Plantenna/Stomata-microscope/IMG_2707.jpg

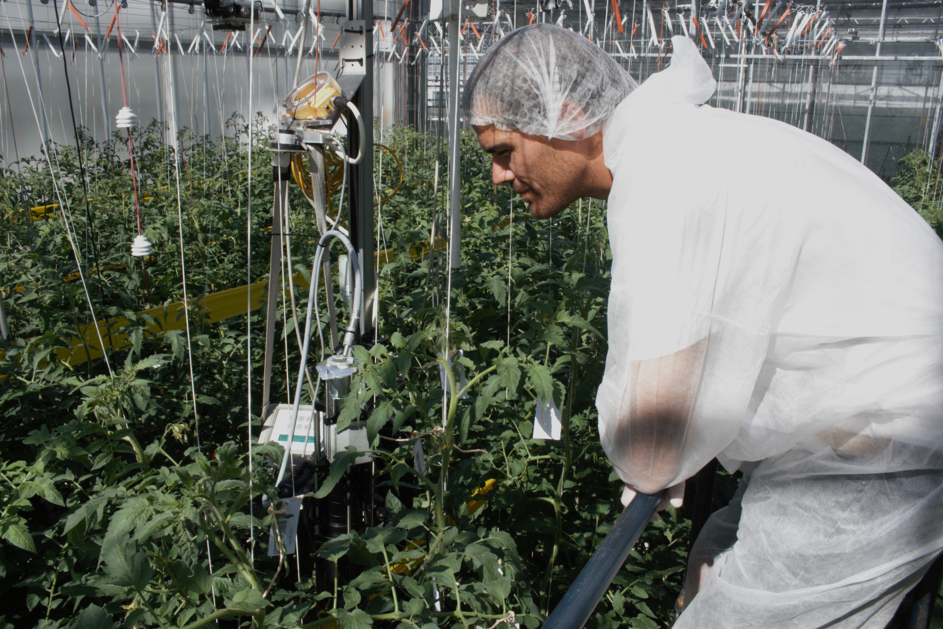
IMG_2707.jpg
