Plantenna/Stomata-microscope/stomata microscope mechanical/3d printed cover.SLDPRT

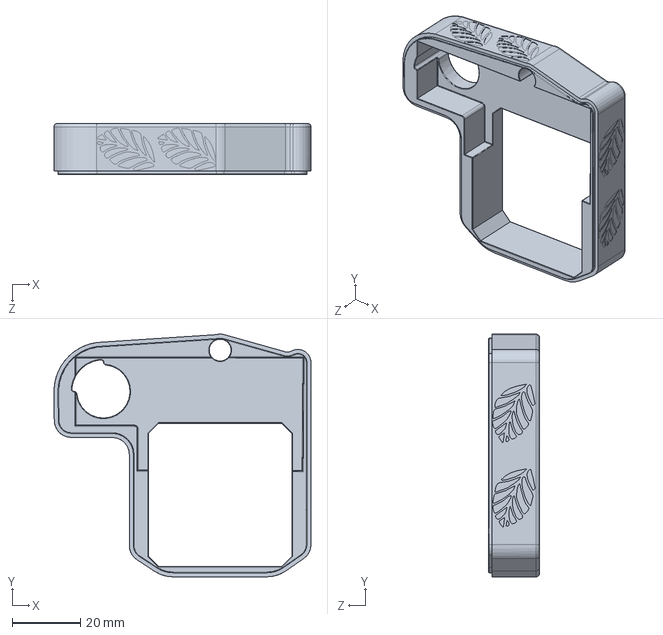
[picture p18: CAD file, 2023-04-05]
stomata microscope mechanical/3d printed cover.SLDPRT
75.3 x 71.1 x 15.0 mm
