Plantenna/Stomata-microscope/stomata microscope mechanical/ER18.sldprt

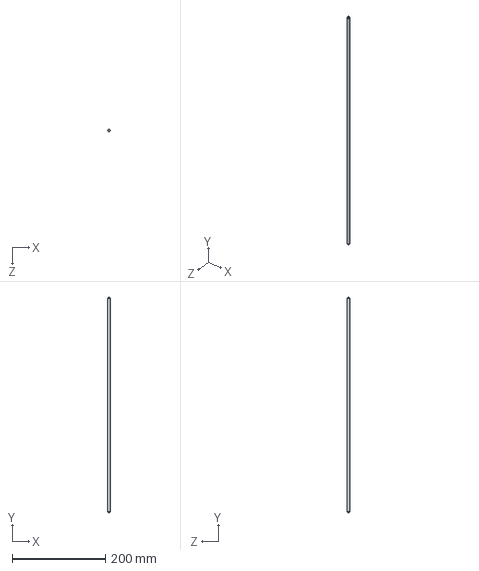
[picture p19: CAD file, 2023-04-05]
stomata microscope mechanical/ER18.sldprt
5.99 x 462.3 x 5.99 mm
