Plantenna/Stomata-microscope/stomata microscope mechanical/SM2L10-Solidworks.sldprt

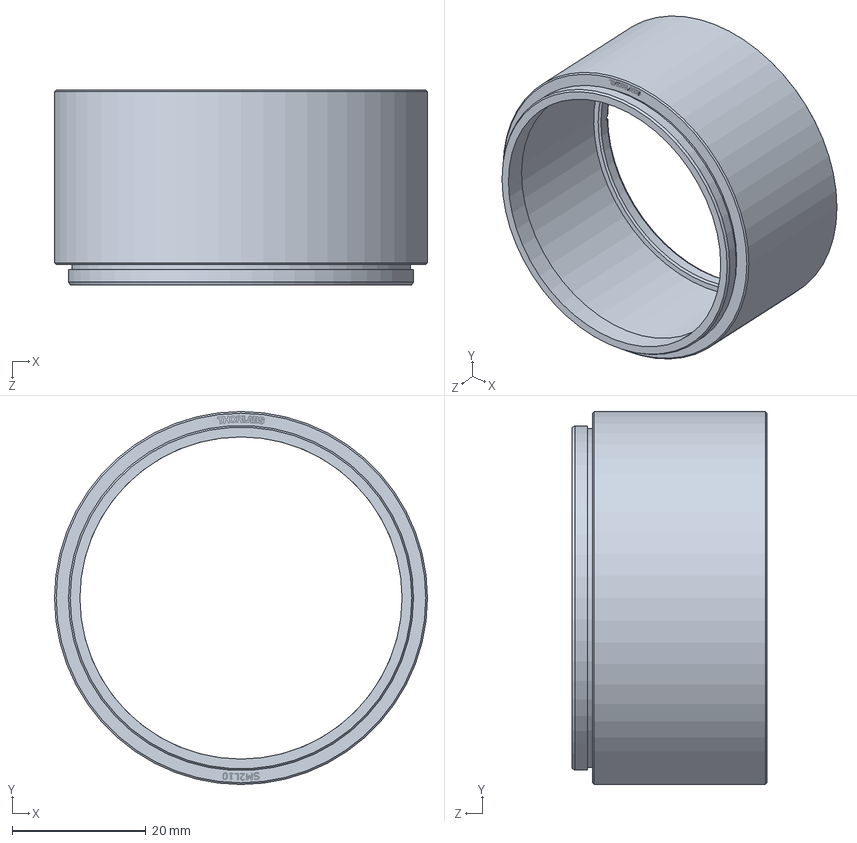
[picture p20: CAD file, 2023-04-05]
stomata microscope mechanical/SM2L10-Solidworks.sldprt
55.9 x 55.9 x 29.2 mm
