Plantenna/Stomata-microscope/stomata microscope mechanical/LCP10_M.sldprt

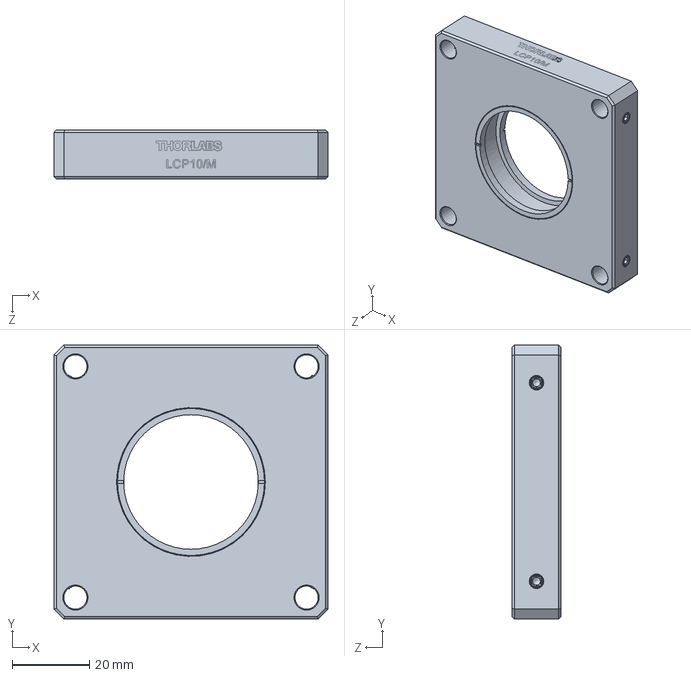
[picture p21: CAD file, 2023-04-05]
stomata microscope mechanical/LCP10_M.sldprt
71.1 x 71.1 x 12.7 mm
