Plantenna/Stomata-microscope/stomata microscope mechanical/SM2V10-Solidworks.sldprt

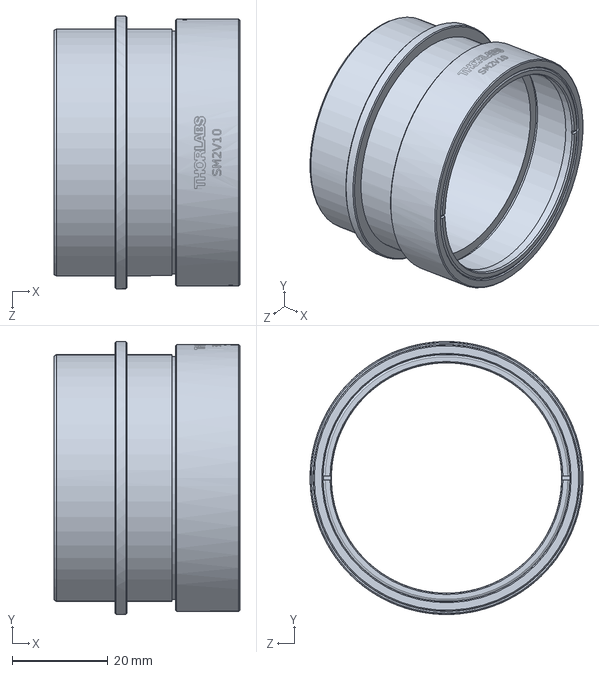
[picture p22: CAD file, 2023-04-05]
stomata microscope mechanical/SM2V10-Solidworks.sldprt
38.9 x 57.1 x 57.1 mm
