Plantenna/Stomata-microscope/stomata microscope mechanical/CT1-tread.SLDPRT

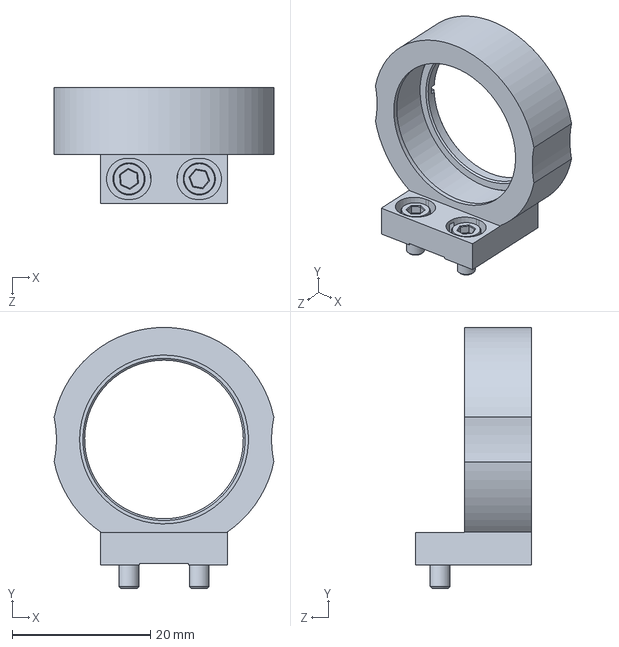
[picture p23: CAD file, 2023-04-05]
stomata microscope mechanical/CT1-tread.SLDPRT
31.7 x 37.7 x 16.8 mm
