Plantenna/Stomata-microscope/stomata microscope mechanical/50X NIR.SLDPRT

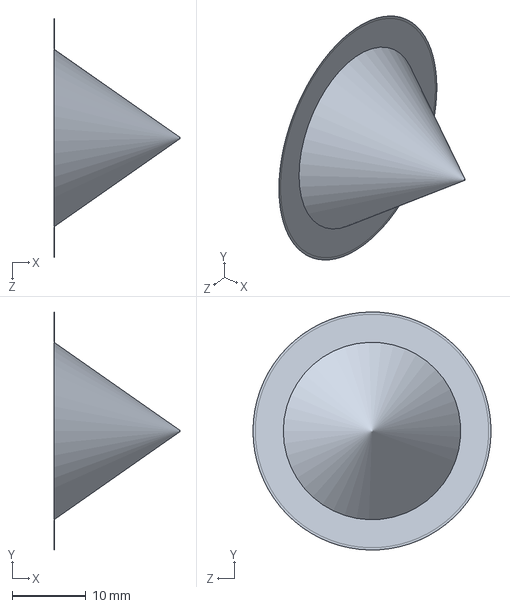
[picture p24: CAD file, 2023-04-05]
stomata microscope mechanical/50X NIR.SLDPRT
17.0 x 32.2 x 32.2 mm
