Plantenna/Stomata-microscope/stomata microscope mechanical/SM2L05-Solidworks.sldprt

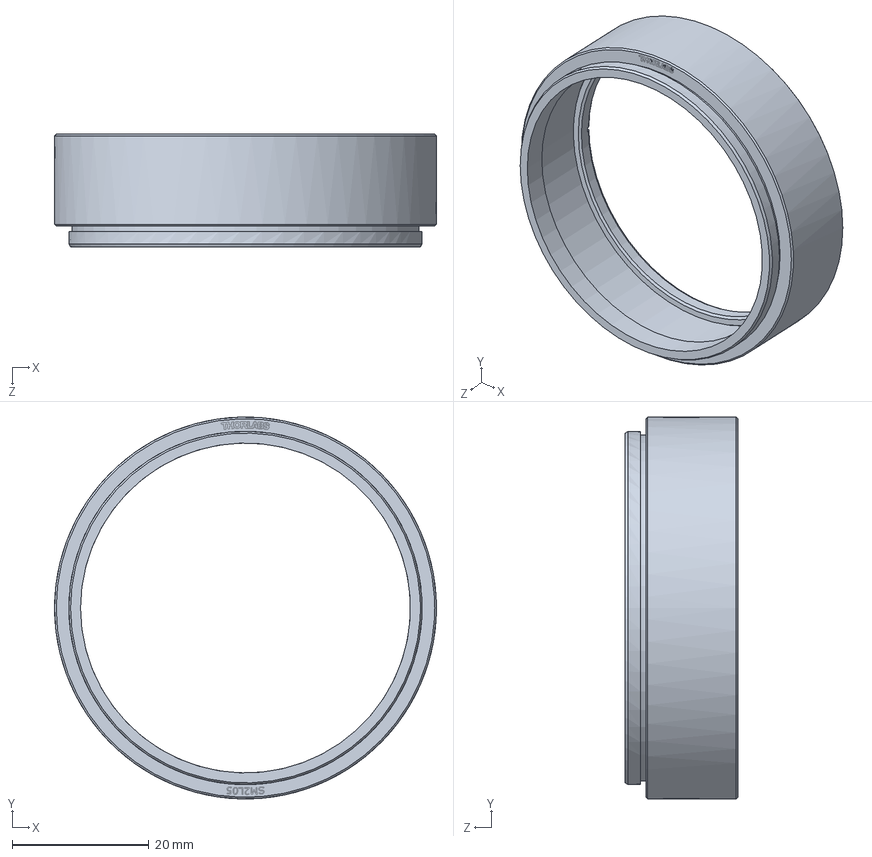
[picture p25: CAD file, 2023-04-05]
stomata microscope mechanical/SM2L05-Solidworks.sldprt
55.9 x 55.9 x 16.5 mm
