Plantenna/Stomata-microscope/stomata microscope mechanical/3d printed cover front.SLDPRT

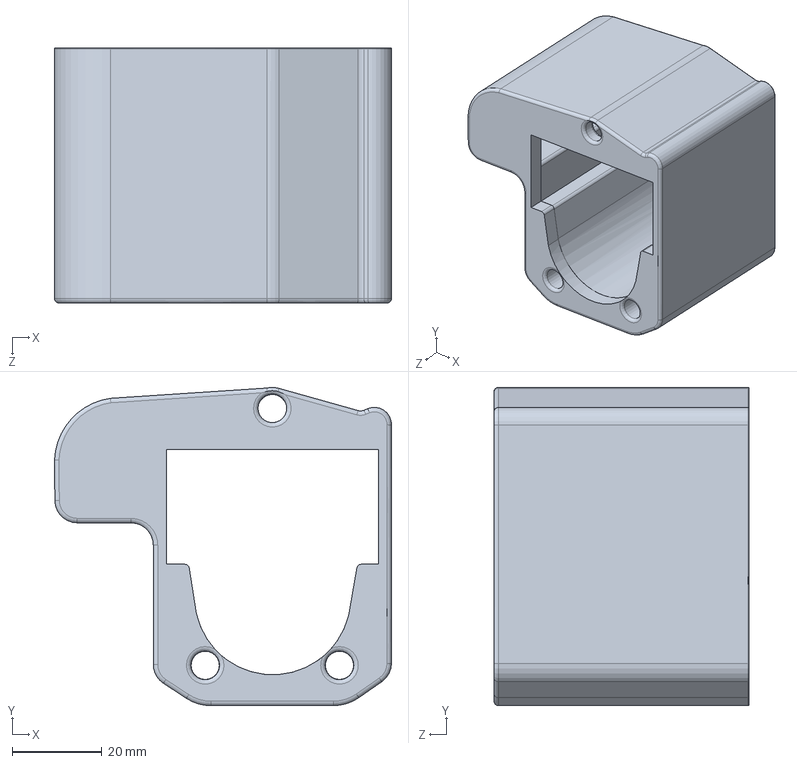
[picture p26: CAD file, 2023-04-05]
stomata microscope mechanical/3d printed cover front.SLDPRT
75.3 x 71.1 x 57.0 mm
