Plantenna/Stomata-microscope/stomata microscope mechanical/LCP33_M-35 mm hole SLDPRT.SLDPRT

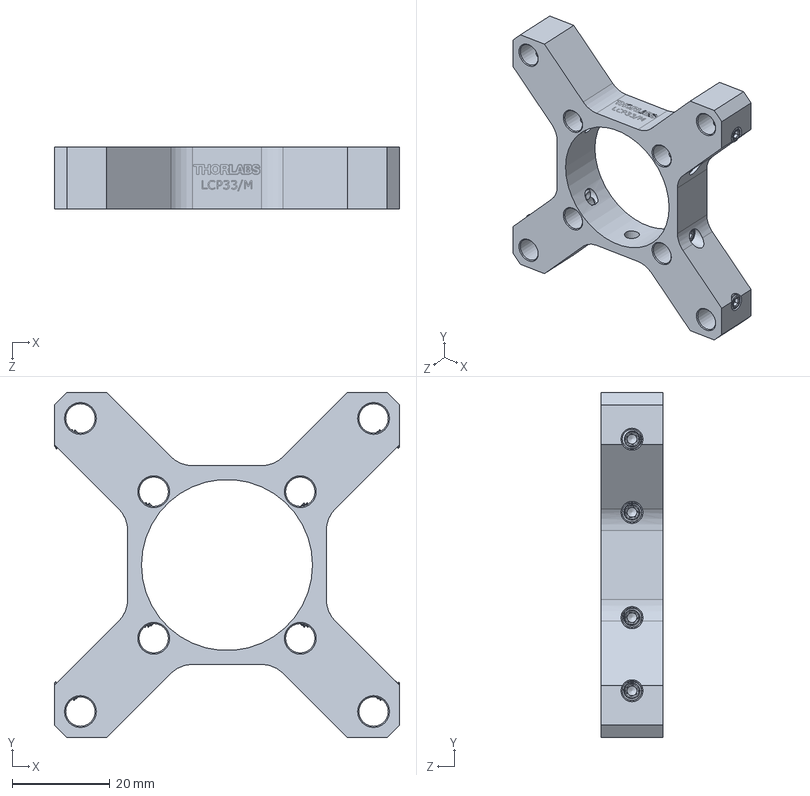
[picture p27: CAD file, 2023-04-05]
stomata microscope mechanical/LCP33_M-35 mm hole SLDPRT.SLDPRT
70.6 x 70.6 x 12.7 mm
