Plantenna/Stomata-microscope/stomata microscope mechanical/BFS-U3.SLDPRT

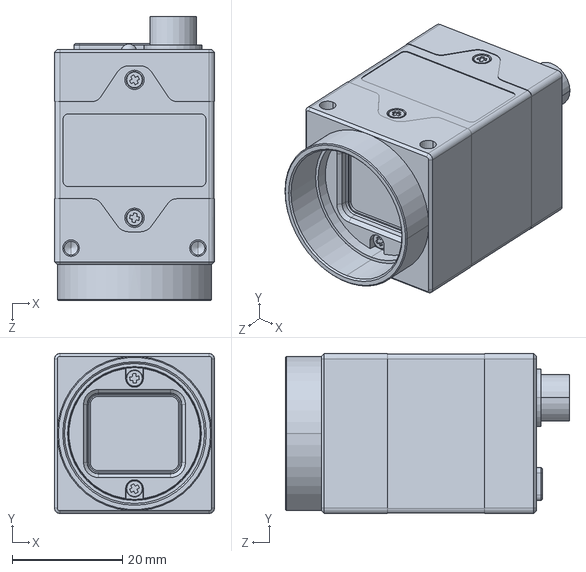
[picture p28: CAD file, 2023-04-05]
stomata microscope mechanical/BFS-U3.SLDPRT
29.0 x 29.0 x 51.5 mm
