Plantenna/Stomata-microscope/stomata microscope mechanical/FB550-40.sldprt

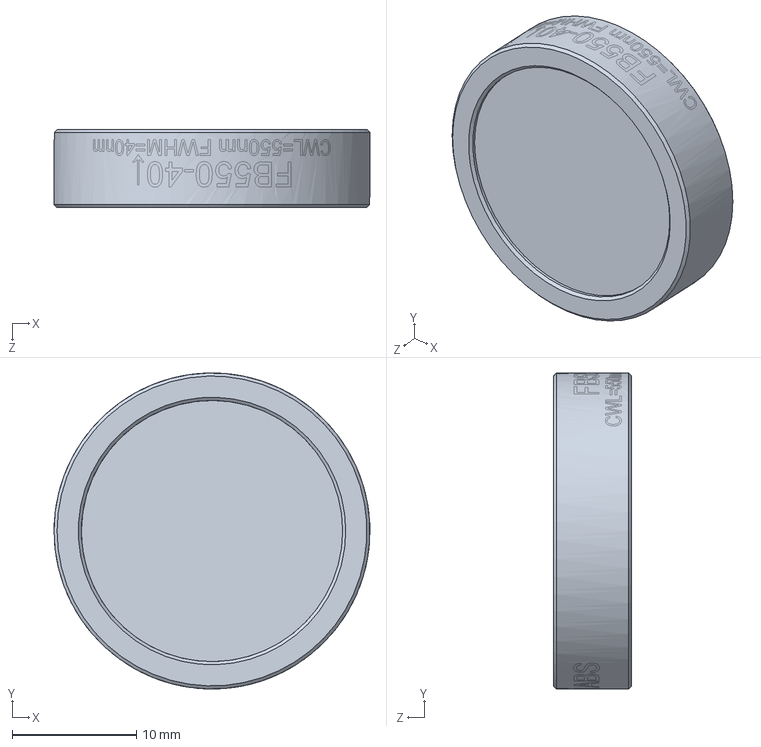
[picture p29: CAD file, 2023-04-05]
stomata microscope mechanical/FB550-40.sldprt
25.4 x 25.4 x 6.30 mm
