Plantenna/Stomata-microscope/stomata microscope mechanical/CT1-slider.SLDPRT

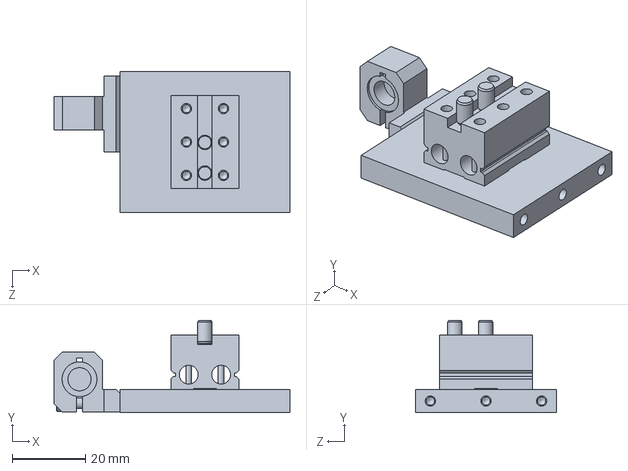
[picture p30: CAD file, 2023-04-05]
stomata microscope mechanical/CT1-slider.SLDPRT
64.6 x 25.3 x 38.6 mm
