Plantenna/Stomata-microscope/stomata microscope mechanical/SM1S10.sldprt

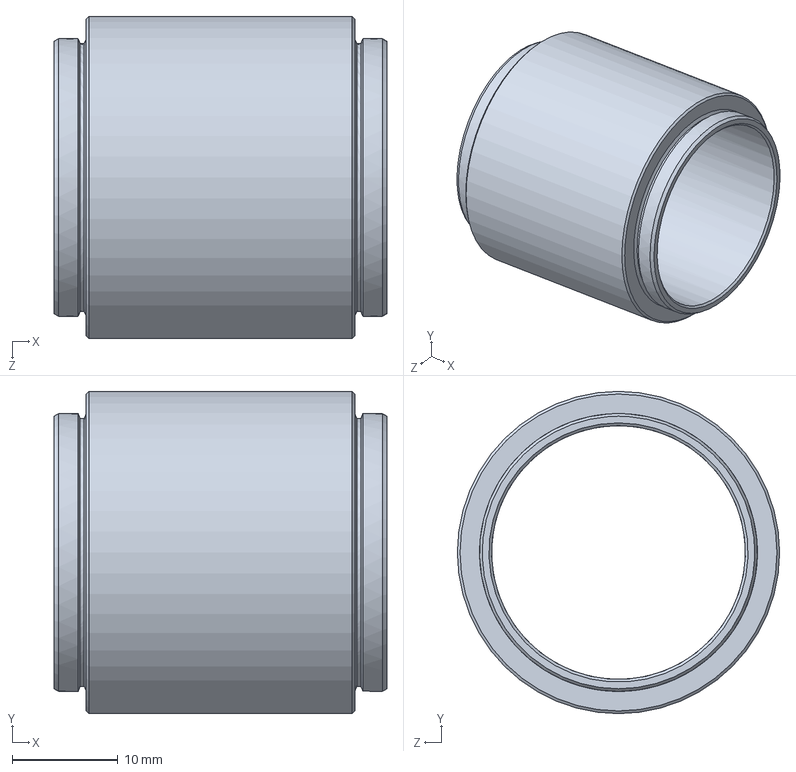
[picture p31: CAD file, 2023-04-05]
stomata microscope mechanical/SM1S10.sldprt
31.5 x 30.5 x 30.5 mm
