Plantenna/Stomata-microscope/stomata microscope mechanical/TTL200-S8-Solidworks.sldprt

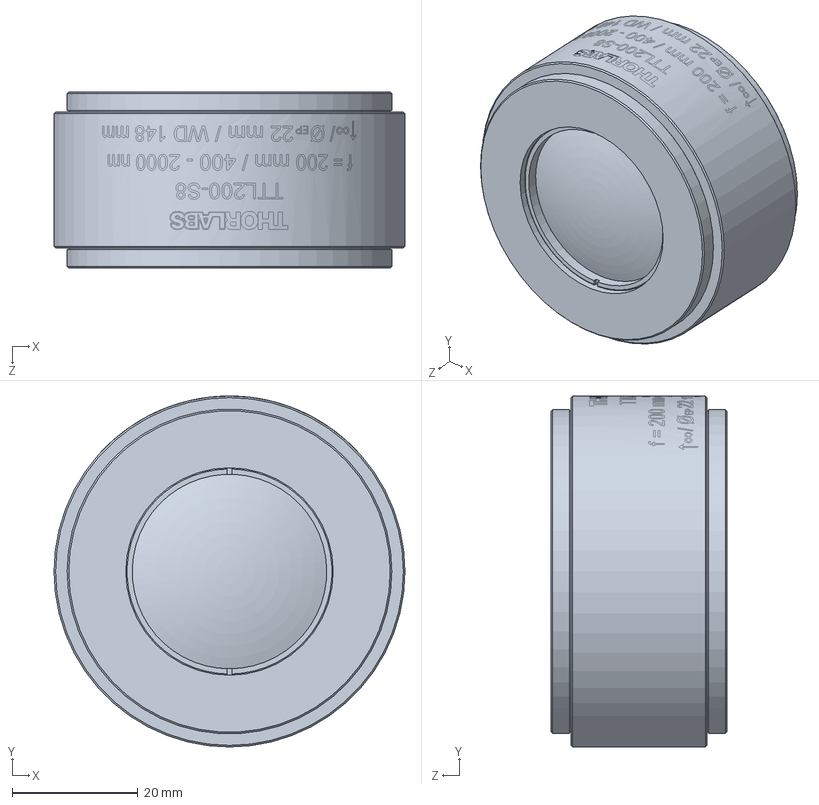
[picture p32: CAD file, 2023-04-05]
stomata microscope mechanical/TTL200-S8-Solidworks.sldprt
55.9 x 55.9 x 28.0 mm
