Plantenna/Stomata-microscope/stomata microscope mechanical/SM1A27.sldprt

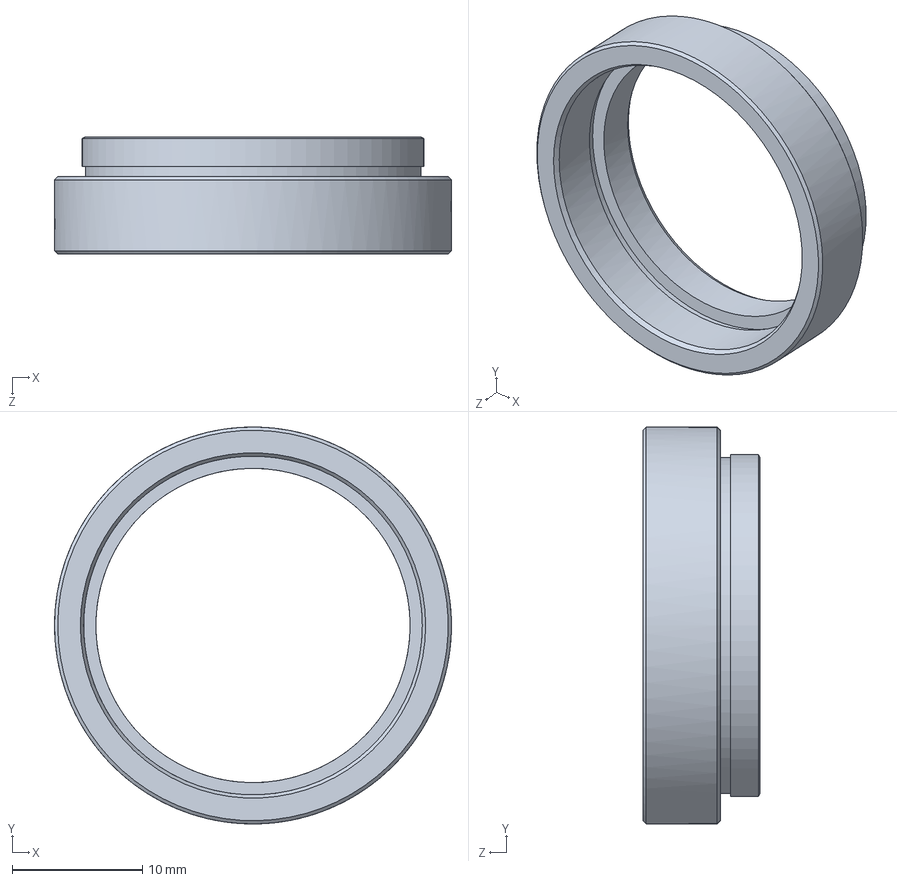
[picture p33: CAD file, 2023-04-05]
stomata microscope mechanical/SM1A27.sldprt
30.5 x 30.5 x 9.02 mm
