Plantenna/Stomata-microscope/stomata microscope mechanical/SM1L03.sldprt

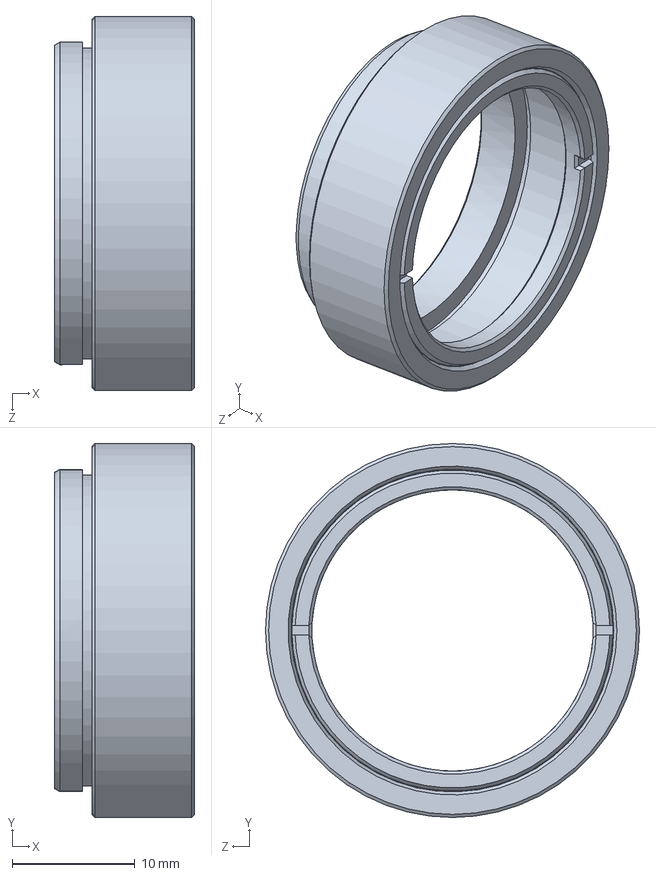
[picture p34: CAD file, 2023-04-05]
stomata microscope mechanical/SM1L03.sldprt
11.4 x 30.5 x 30.5 mm
