Plantenna/Stomata-microscope/stomata microscope mechanical/SM1A2-Solidworks.sldprt

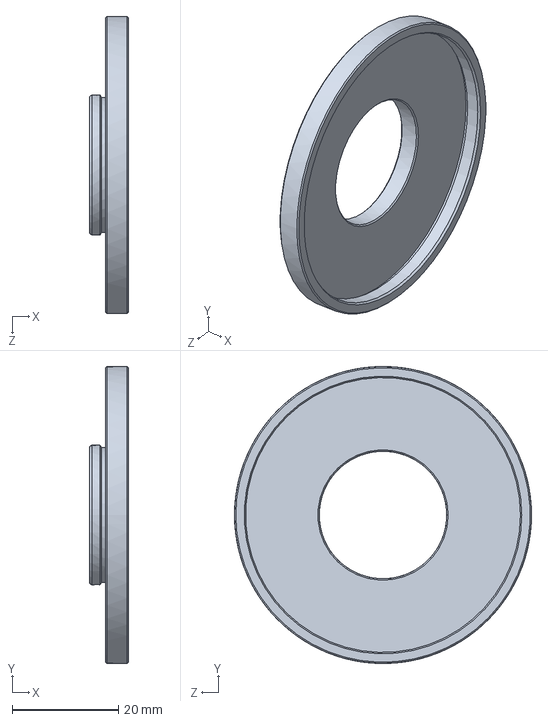
[picture p35: CAD file, 2023-04-05]
stomata microscope mechanical/SM1A2-Solidworks.sldprt
7.37 x 55.9 x 55.9 mm
